prunkdump/GNUVario-TTGO-T5/boitier 3D/Ecran 1.54''/Plan boitier GNU VARIO.pdf

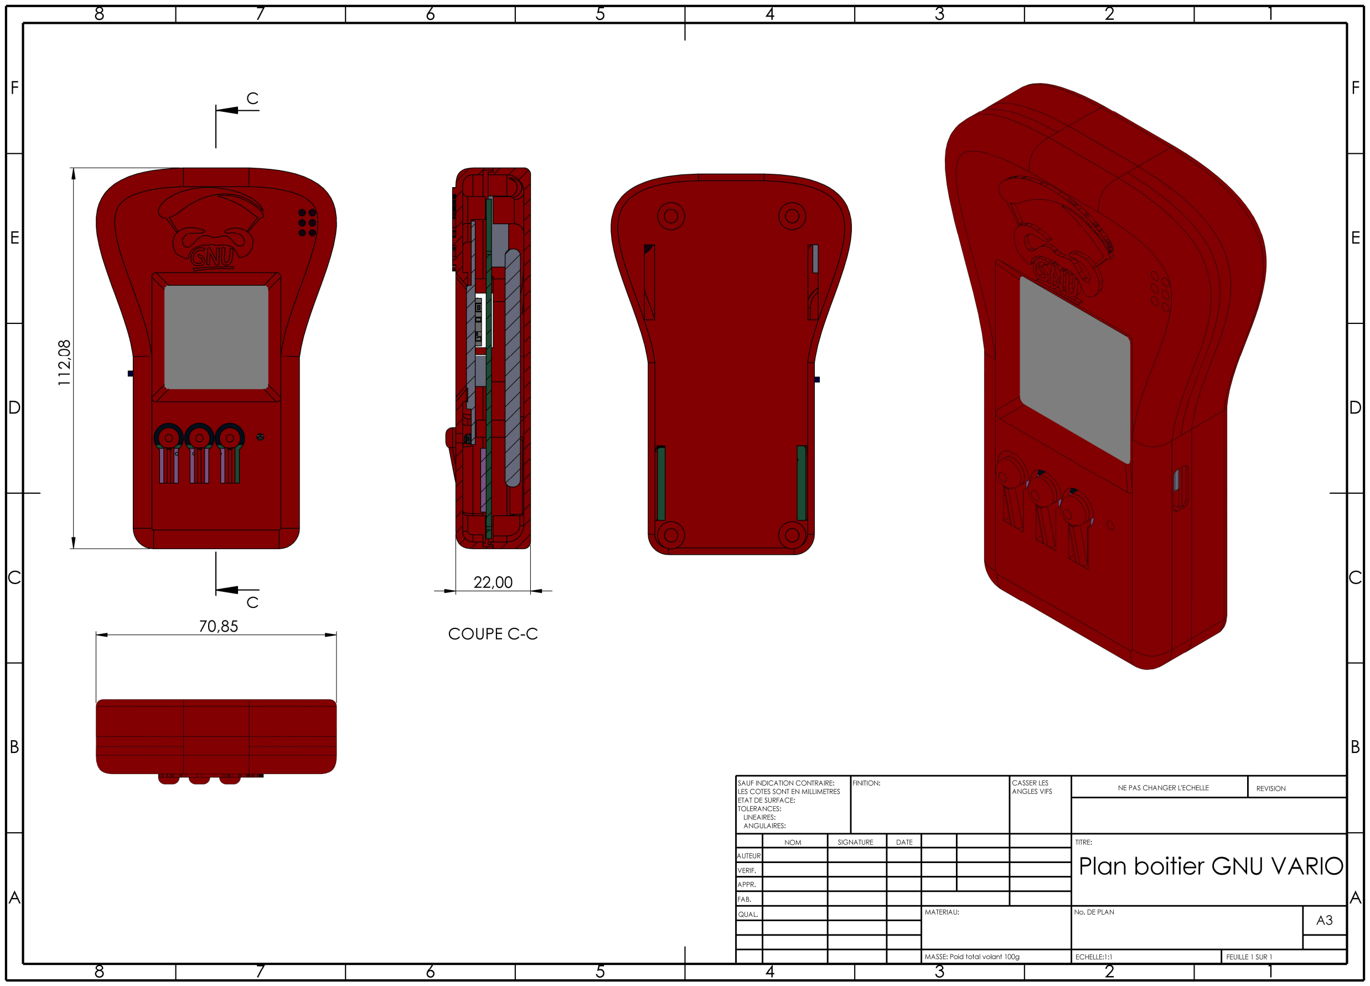
[picture p13: page 1]
