prunkdump/GNUVario-TTGO-T5/boitier 3D/Ecran 1.54''/20190728_134155_resized.jpg

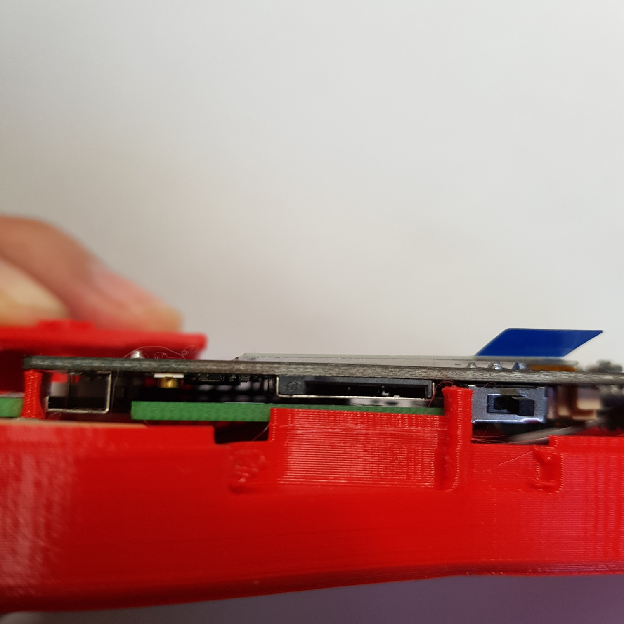
boitier 3D/Ecran 1.54''/20190728_134155_resized.jpg
