prunkdump/GNUVario-TTGO-T5/boitier 3D/Ecran 1.54''/Boitier arrière.jpg

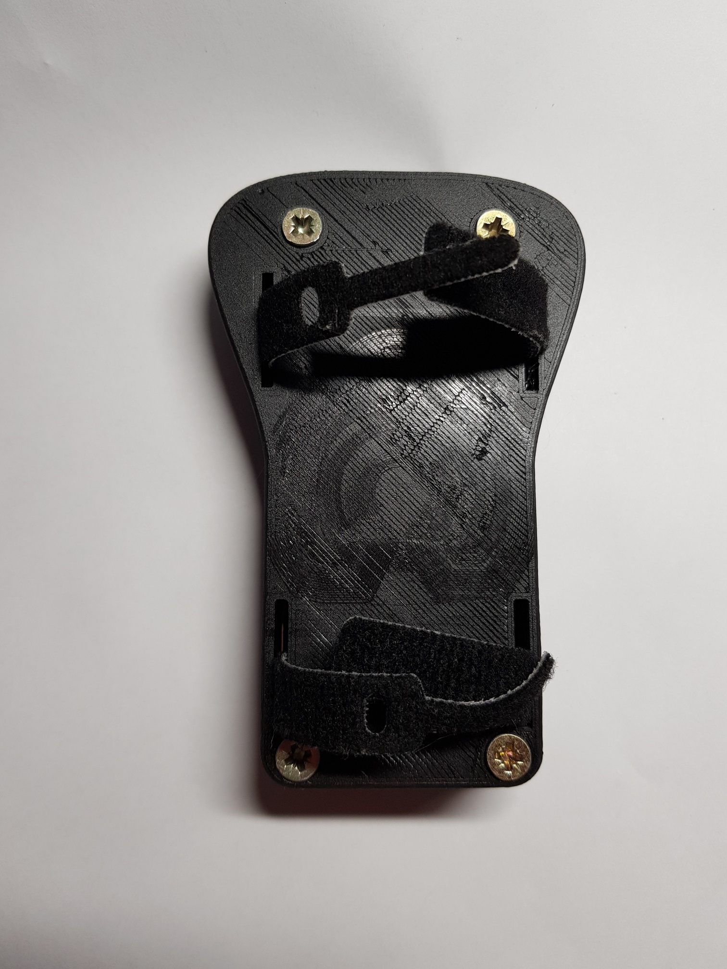
boitier 3D/Ecran 1.54''/Boitier arrière.jpg
