prunkdump/GNUVario-TTGO-T5/boitier 3D/Ecran 1.54''/Boitier avant.jpg

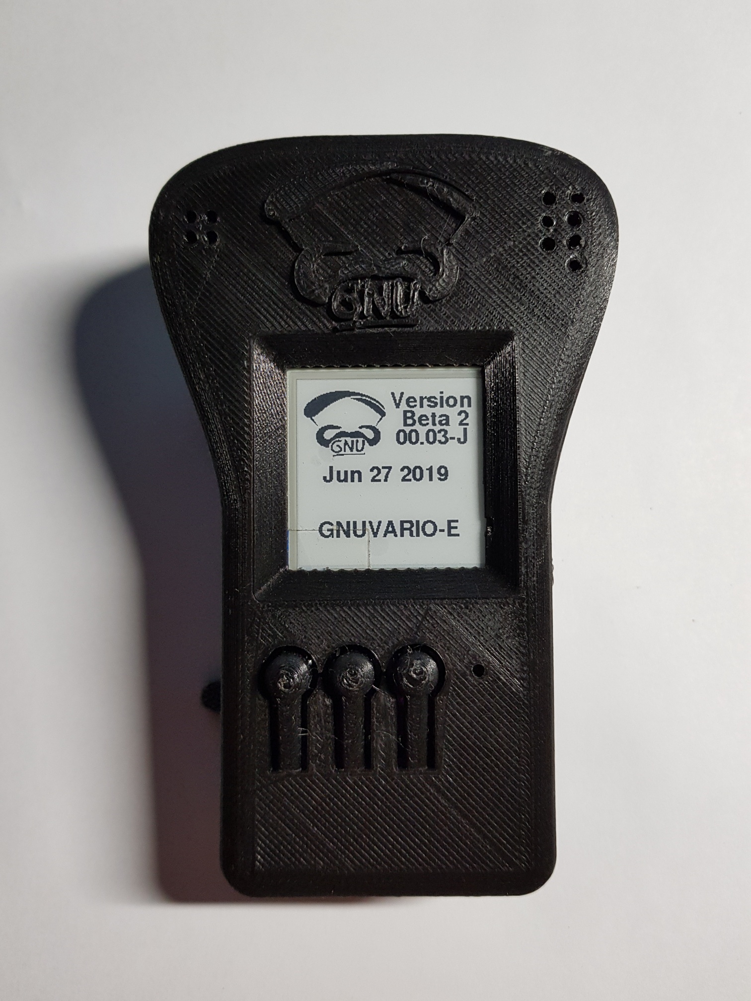
boitier 3D/Ecran 1.54''/Boitier avant.jpg
