prunkdump/GNUVario-TTGO-T5/boitier 3D/Ecran 1.54''/boitier tranche.jpg

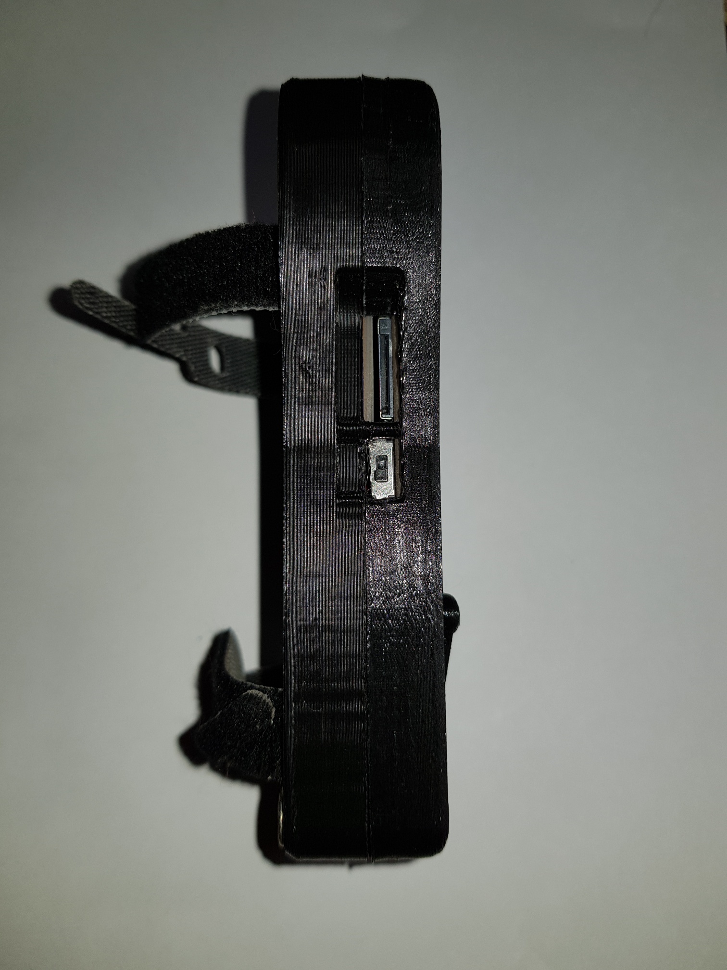
boitier 3D/Ecran 1.54''/boitier tranche.jpg
