prunkdump/GNUVario-TTGO-T5/boitier 3D/Ecran 1.54''/Fashion week.jpg

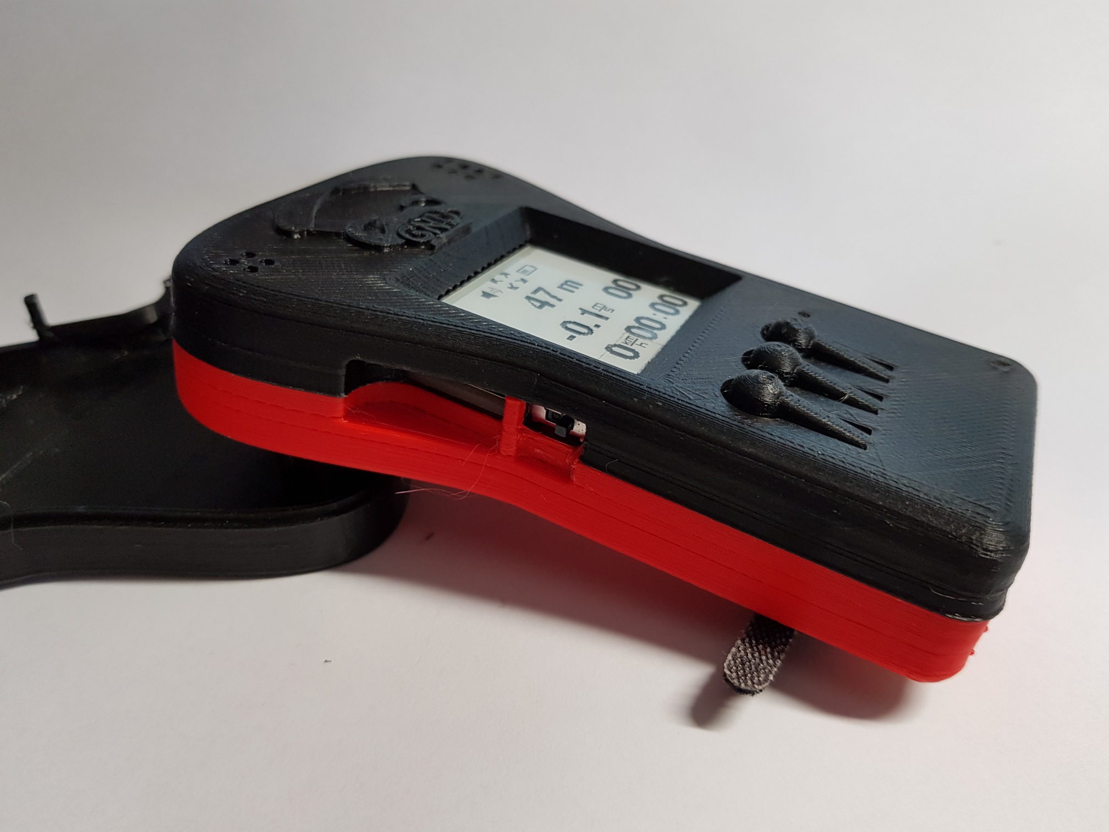
boitier 3D/Ecran 1.54''/Fashion week.jpg
