prunkdump/GNUVario-TTGO-T5/boitier 3D/Ecran 1.54''/Gnu bottom case/vis plastique.jpg

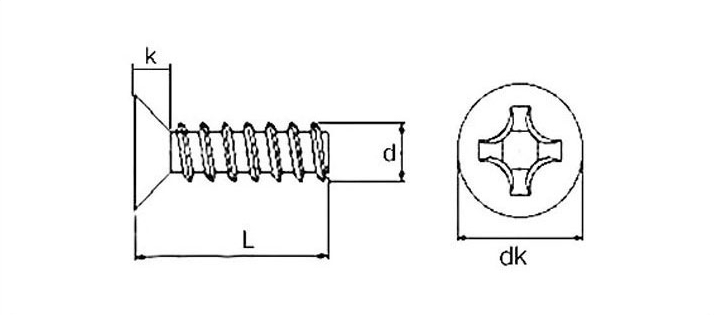
boitier 3D/Ecran 1.54''/Gnu bottom case/vis plastique.jpg
