prunkdump/GNUVario-TTGO-T5/boitier 3D/Ecran 1.54''/Support carte antenne.jpg

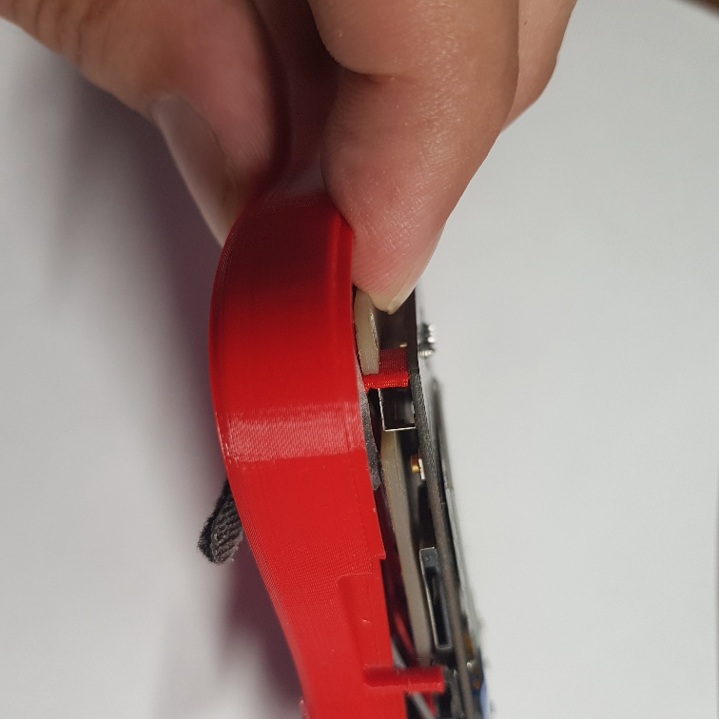
boitier 3D/Ecran 1.54''/Support carte antenne.jpg
