prunkdump/GNUVario-TTGO-T5/boitier 3D/Ecran 1.54''/Support carte pour soulager les boutons.jpg

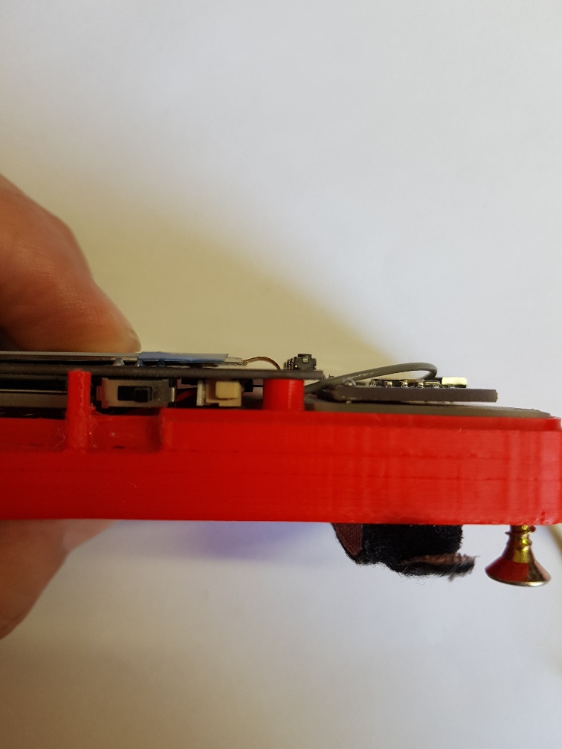
boitier 3D/Ecran 1.54''/Support carte pour soulager les boutons.jpg
