prunkdump/GNUVario-TTGO-T5/boitier 3D/Ecran 2.9'' portrait/Boitier 2.9 élévateurs.jpg

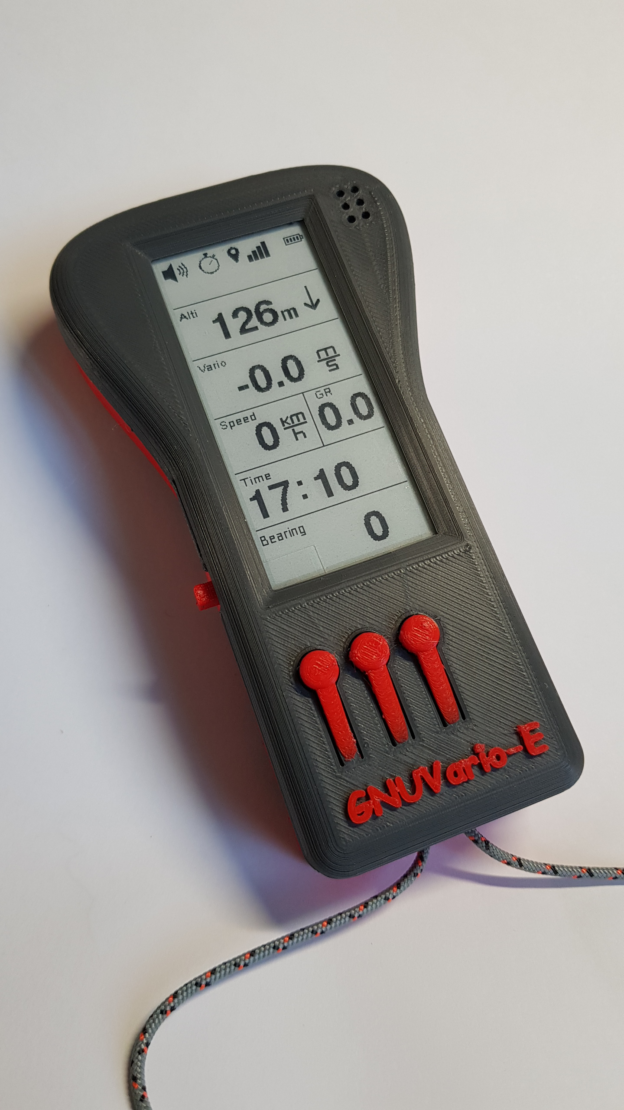
boitier 3D/Ecran 2.9'' portrait/Boitier 2.9 élévateurs.jpg
