prunkdump/GNUVario-TTGO-T5/boitier 3D/Ecran 2.9''/thumbnail_20190925_140538_resized.jpg

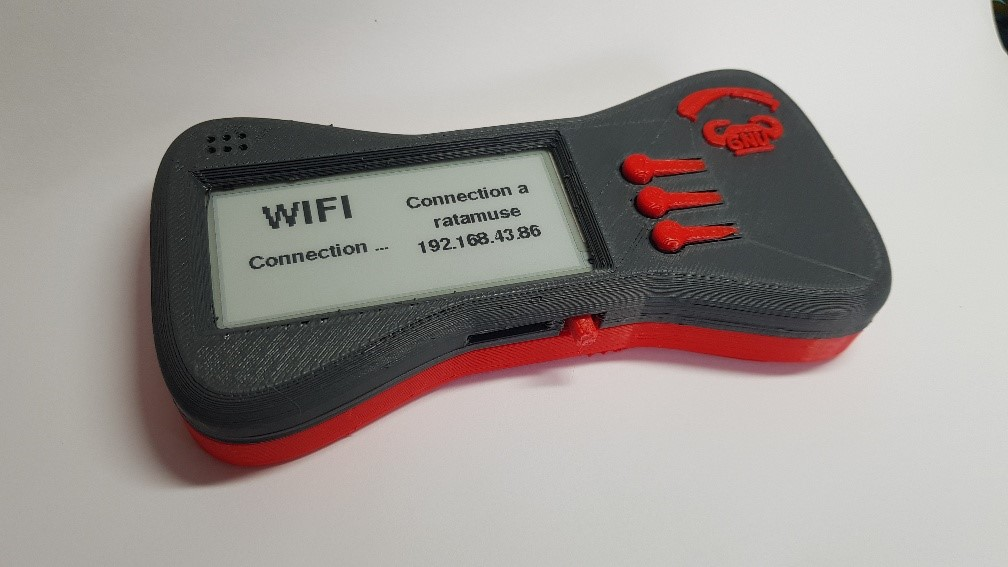
boitier 3D/Ecran 2.9''/thumbnail_20190925_140538_resized.jpg
