prunkdump/GNUVario-TTGO-T5/boitier 3D/Ecran 2.9''/thumbnail_20190925_141046_resized.jpg

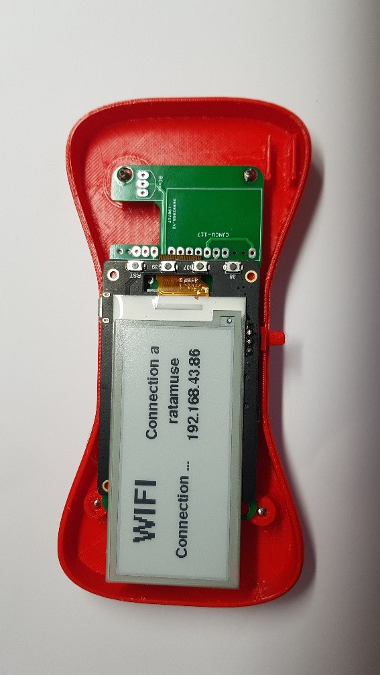
boitier 3D/Ecran 2.9''/thumbnail_20190925_141046_resized.jpg
