prunkdump/GNUVario-TTGO-T5/PCB/20191011_115533_resized.jpg

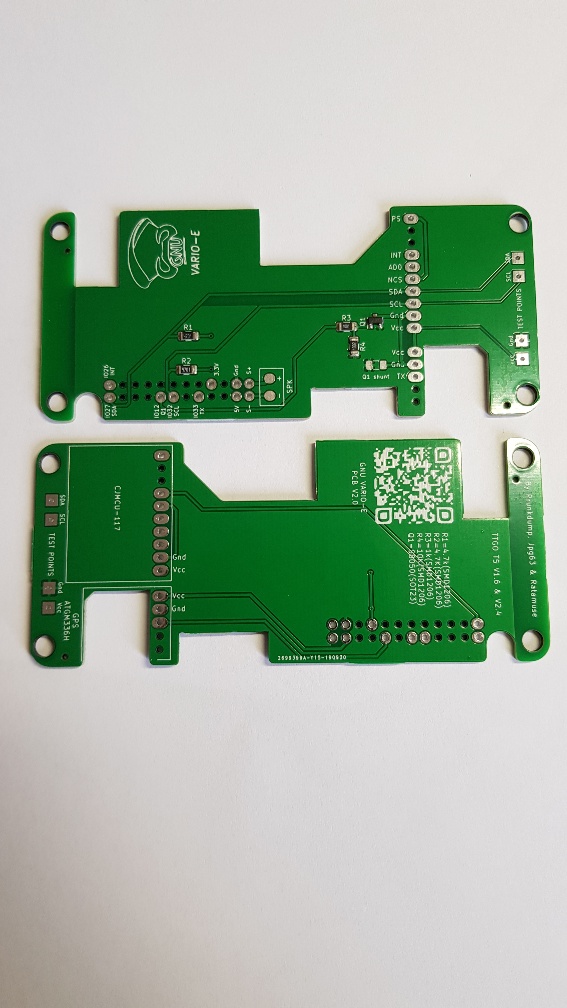
PCB/20191011_115533_resized.jpg
