prunkdump/GNUVario-TTGO-T5/PCB/Gnu Vario TTGO T5 V2 back.jpg

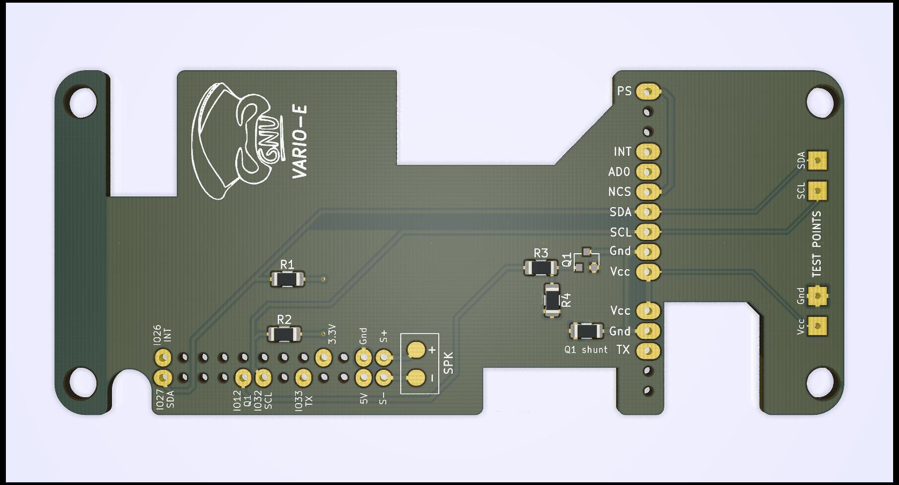
PCB/Gnu Vario TTGO T5 V2 back.jpg
