prunkdump/GNUVario-TTGO-T5/PCB/Gnu Vario TTGO T5 V2 front.jpg

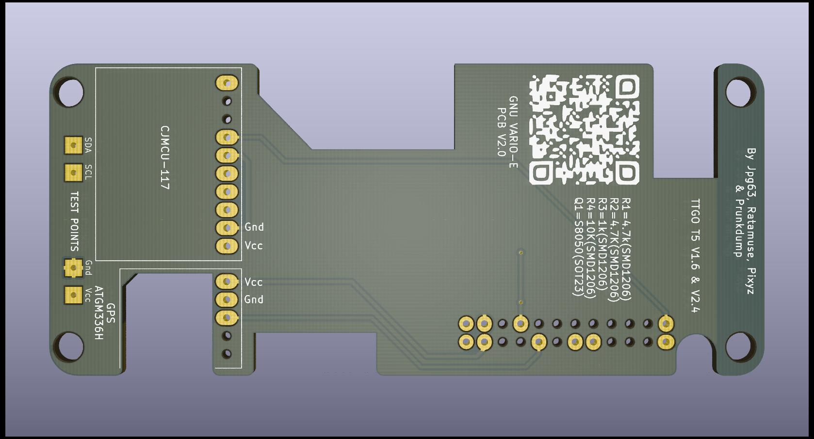
PCB/Gnu Vario TTGO T5 V2 front.jpg
