prunkdump/GNUVario-TTGO-T5/PCB/KiCad GNU Vario E V1.12/Pictures/PCB Back.jpeg

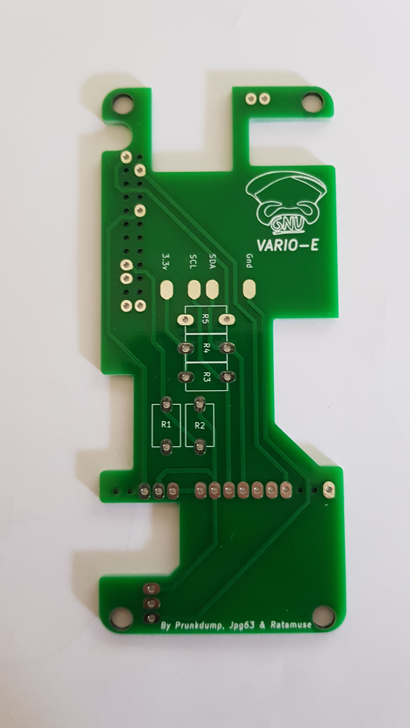
PCB/KiCad GNU Vario E V1.12/Pictures/PCB Back.jpeg
