prunkdump/GNUVario-TTGO-T5/PCB/PCB arrière.jpg

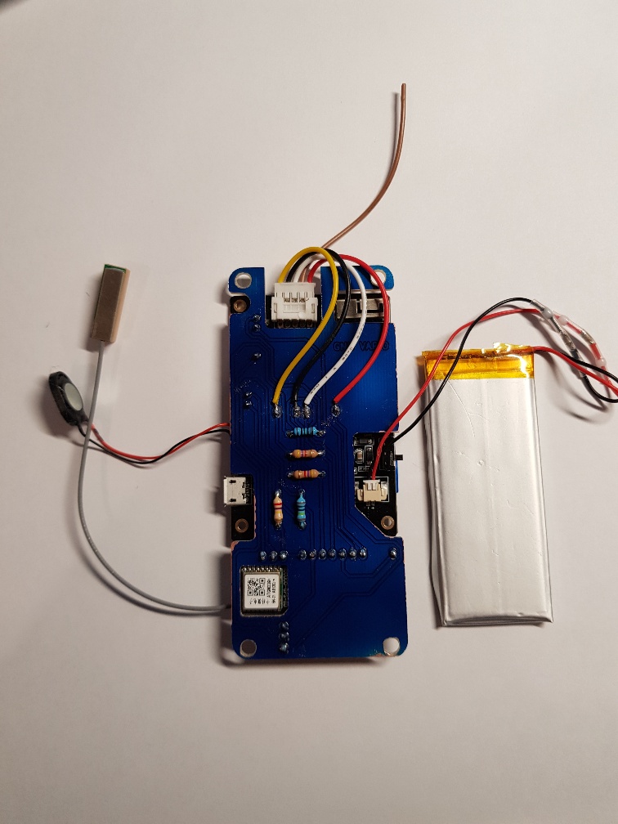
PCB/PCB arrière.jpg
