prunkdump/GNUVario-TTGO-T5/PCB/PCB avant.jpg

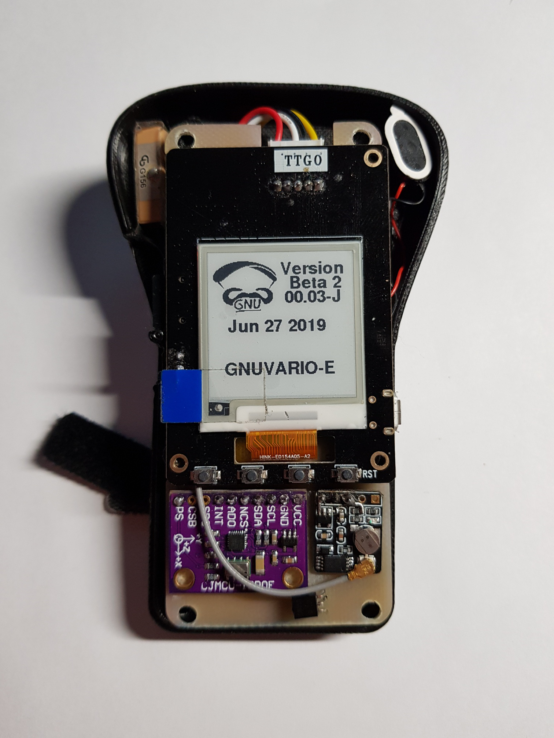
PCB/PCB avant.jpg
