prunkdump/GNUVario-TTGO-T5/PCB/PCB back.jpg

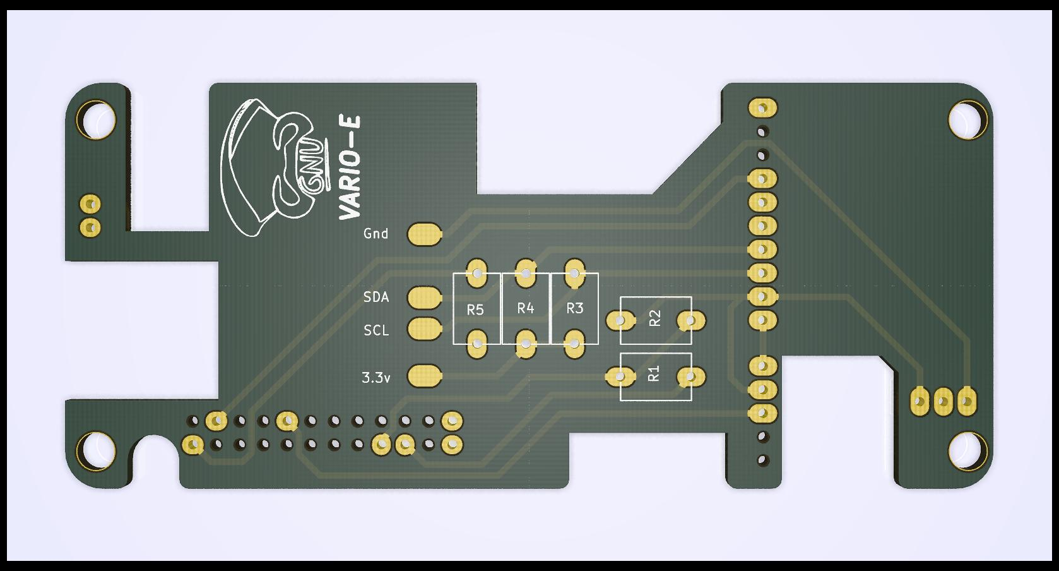
PCB/PCB back.jpg
