prunkdump/GNUVario-TTGO-T5/PCB/PCB front.jpg

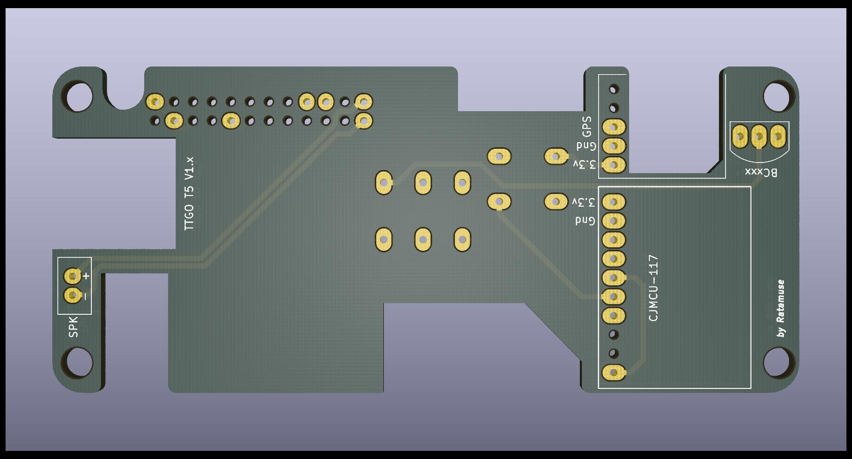
PCB/PCB front.jpg
