prunkdump/GNUVario-TTGO-T5/PCB/placement transistor.jpg

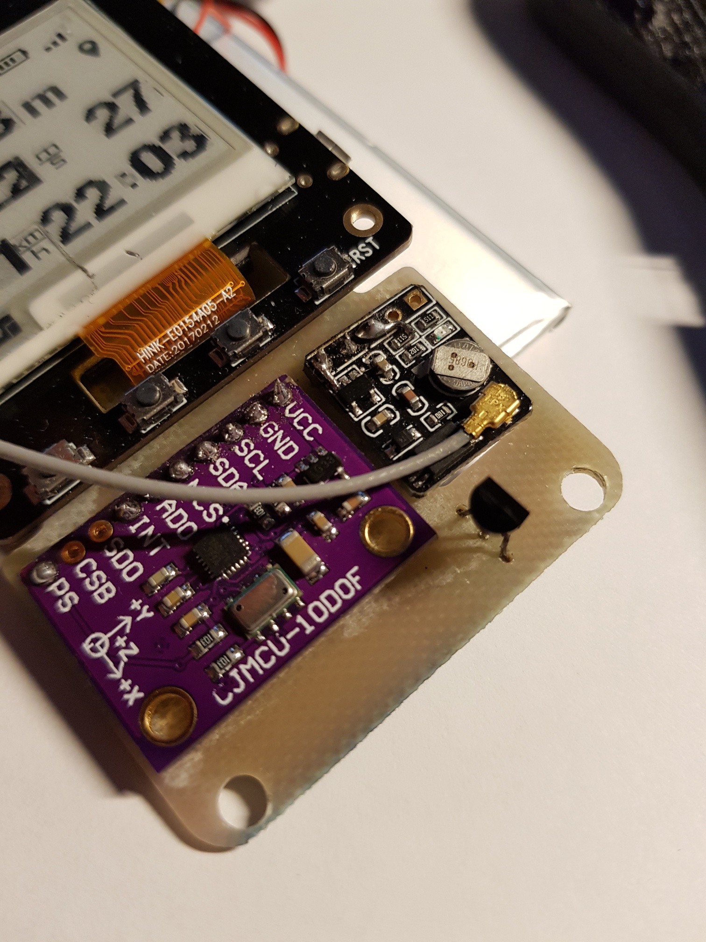
PCB/placement transistor.jpg
