prunkdump/GNUVario-TTGO-T5/Photos/20191012_085850.jpg

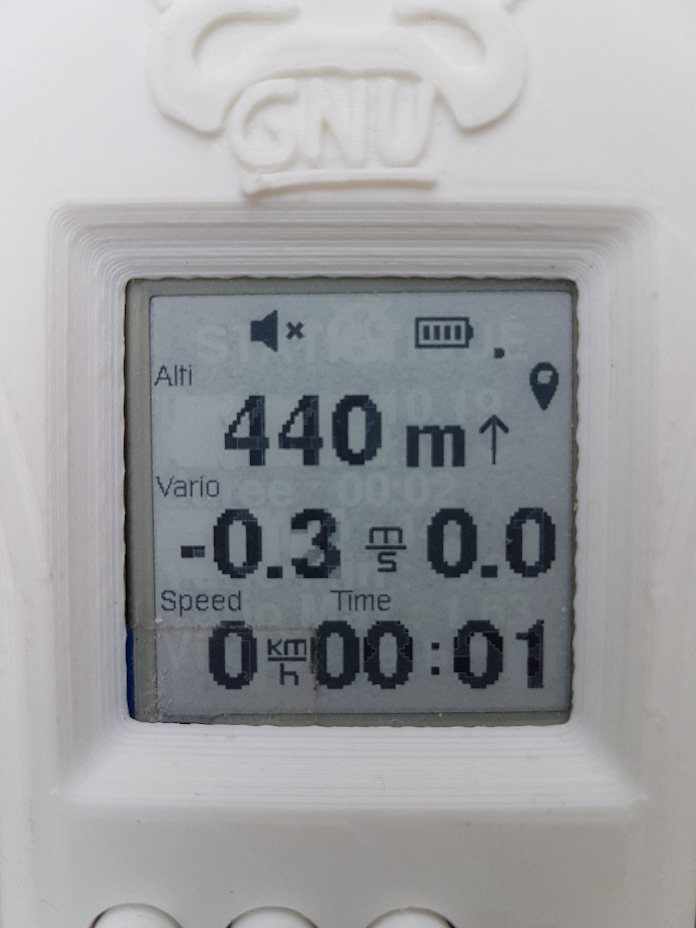
Photos/20191012_085850.jpg
