prunkdump/GNUVario-TTGO-T5/Photos/Case/20190922_080627.jpg

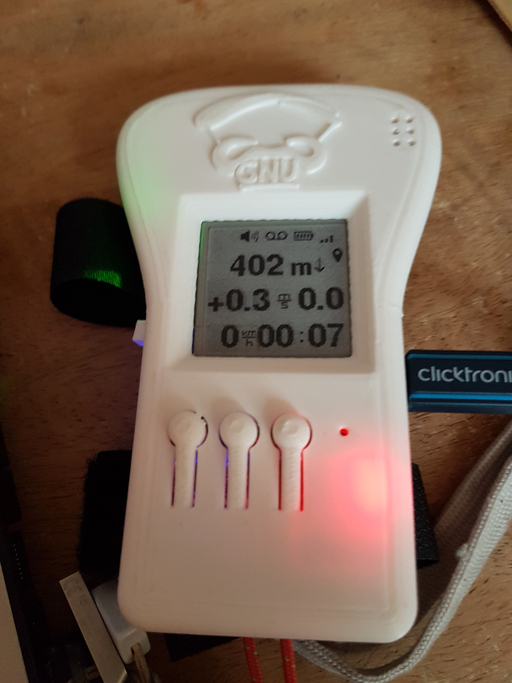
Photos/Case/20190922_080627.jpg
