prunkdump/GNUVario-TTGO-T5/Photos/Case/20191103_104739_resized.jpg

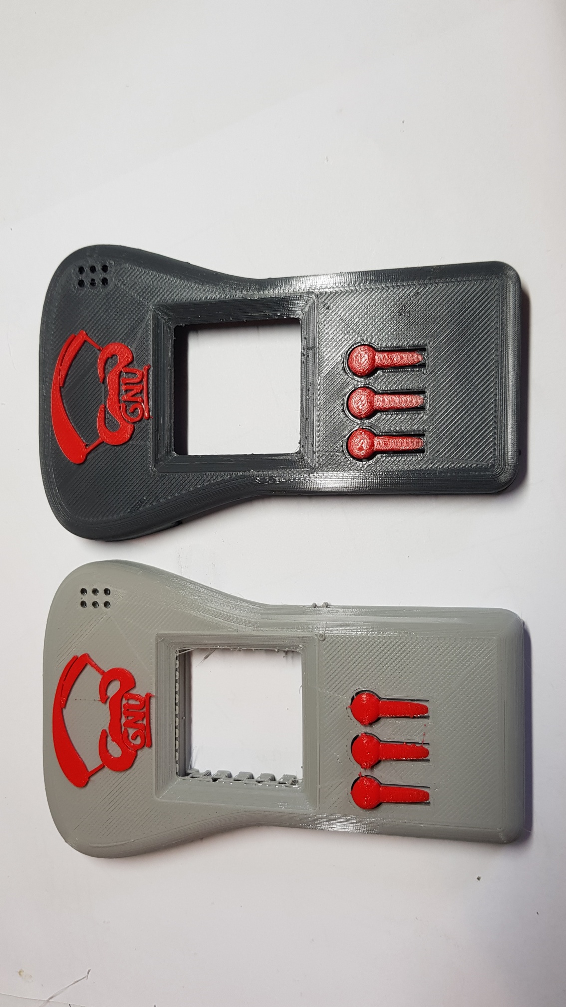
Photos/Case/20191103_104739_resized.jpg
