prunkdump/GNUVario-TTGO-T5/Photos/Case/20191105_001156_resized.jpg

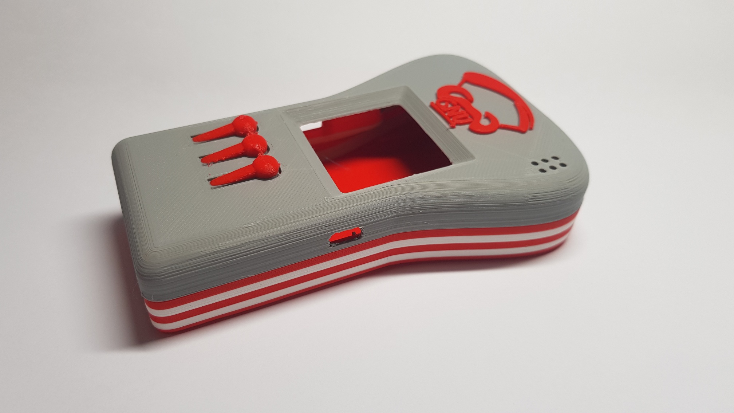
Photos/Case/20191105_001156_resized.jpg
