prunkdump/GNUVario-TTGO-T5/Photos/Case/20191105_001506_resized.jpg

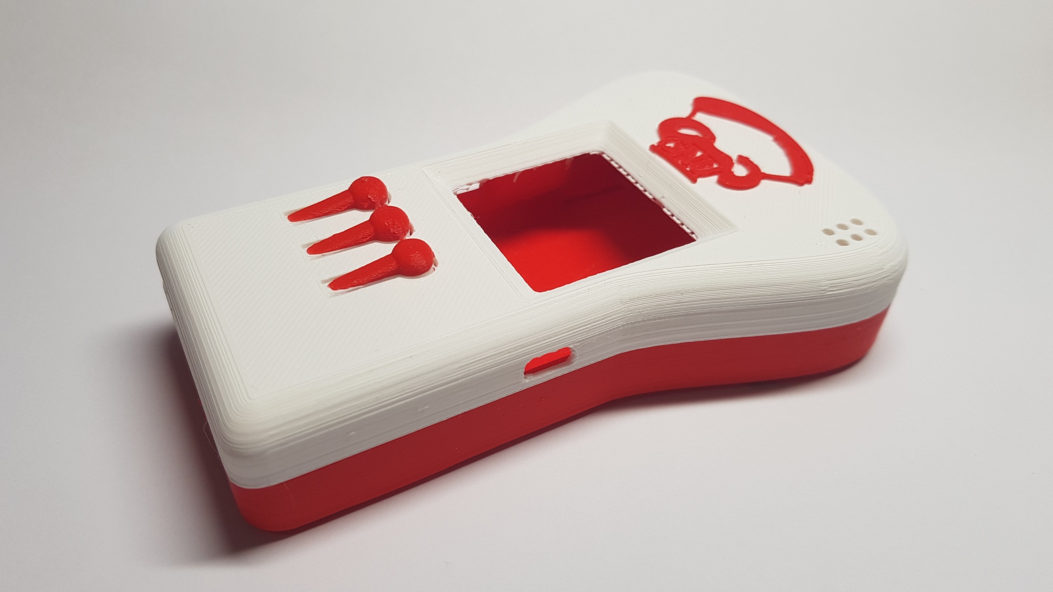
Photos/Case/20191105_001506_resized.jpg
