prunkdump/GNUVario-TTGO-T5/Photos/Case/Fashion week Rouge gris.jpg

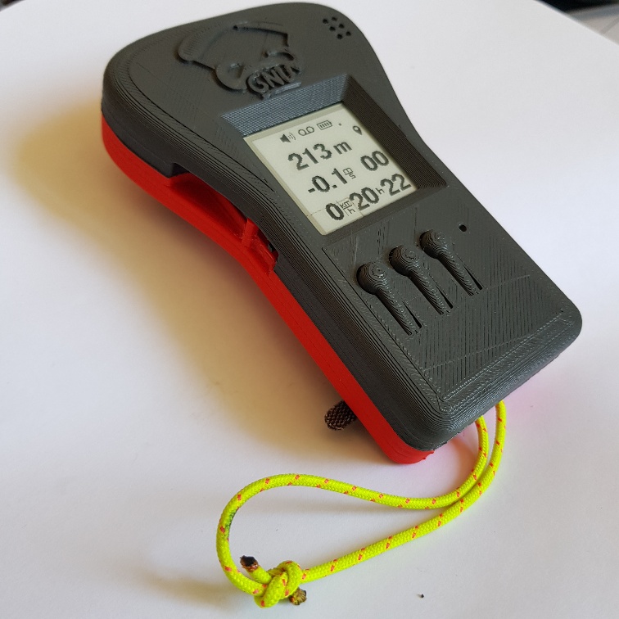
Photos/Case/Fashion week Rouge gris.jpg
