prunkdump/GNUVario-TTGO-T5/Photos/V1/20190727_112918.jpg

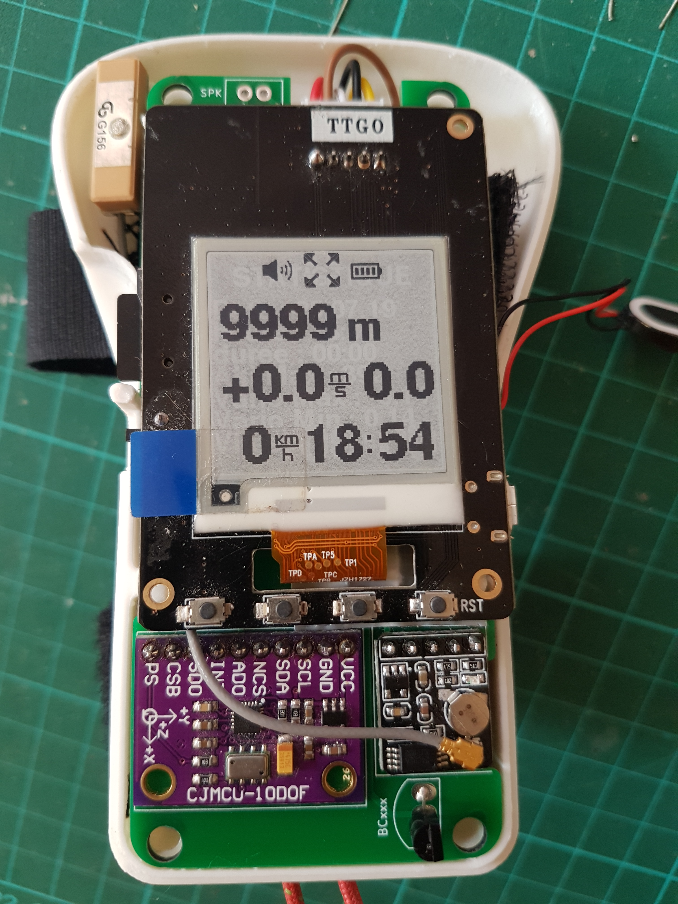
Photos/V1/20190727_112918.jpg
