prunkdump/GNUVario-TTGO-T5/PCB/PCB soldered.jpg

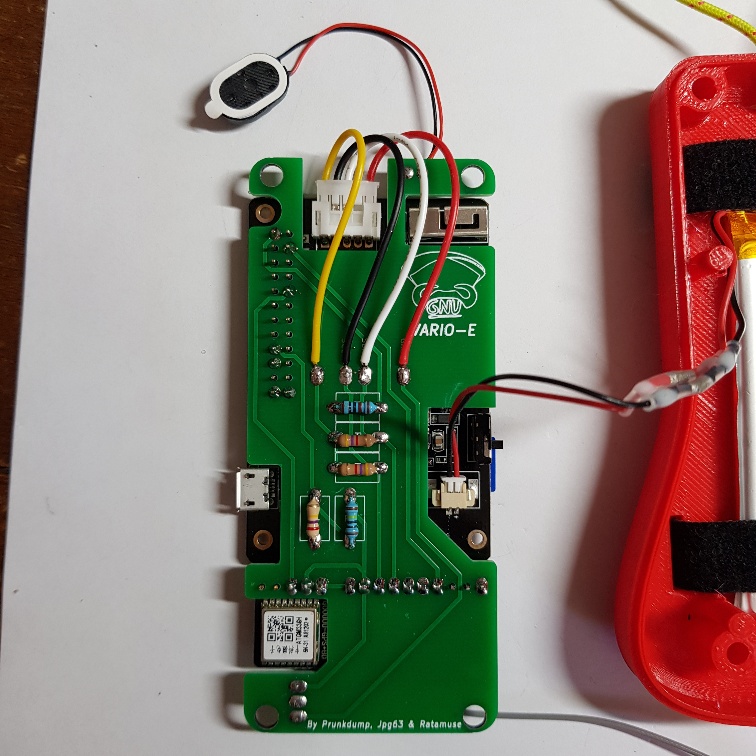
PCB/PCB soldered.jpg
