prunkdump/GNUVario-TTGO-T5/PCB/Printing Impression Schématique.jpg

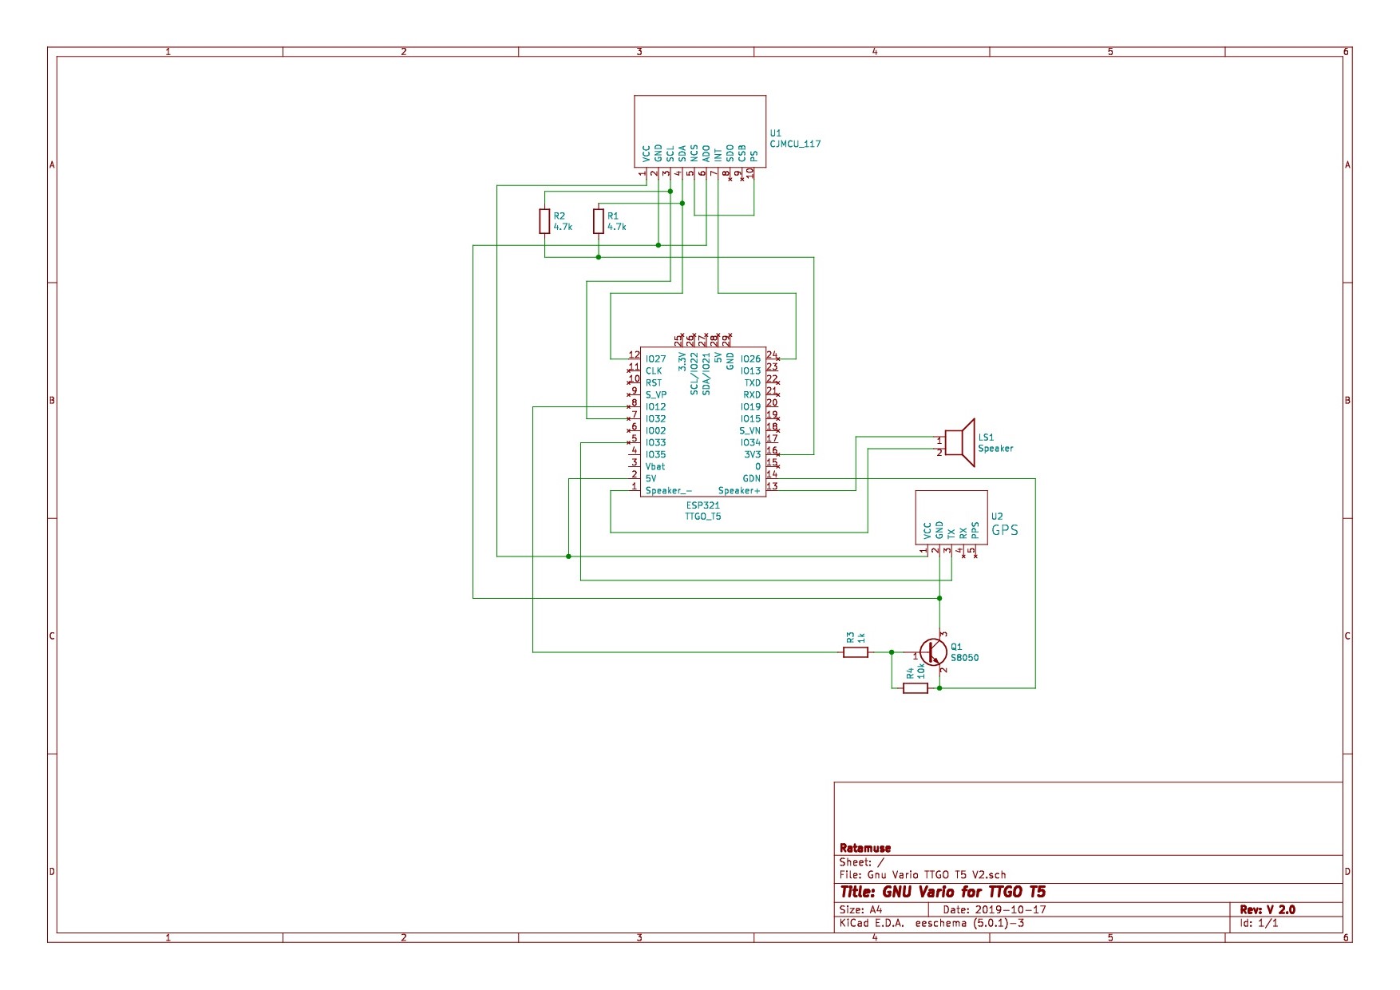
PCB/Printing Impression Schématique.jpg
