prunkdump/GNUVario-TTGO-T5/PCB/PCB V1.10.pdf

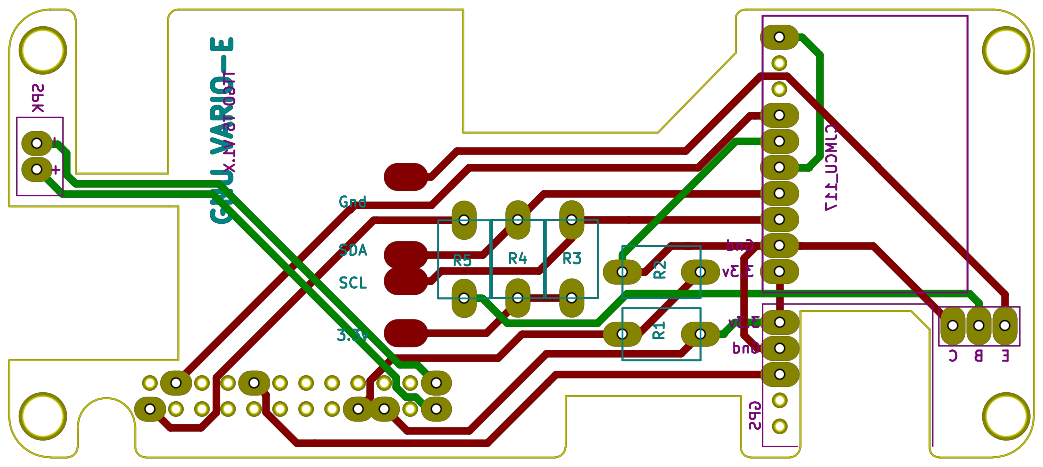
[picture p97: page 1]
