prunkdump/GNUVario-TTGO-T5/PCB/Schéma filaire PCB.pdf

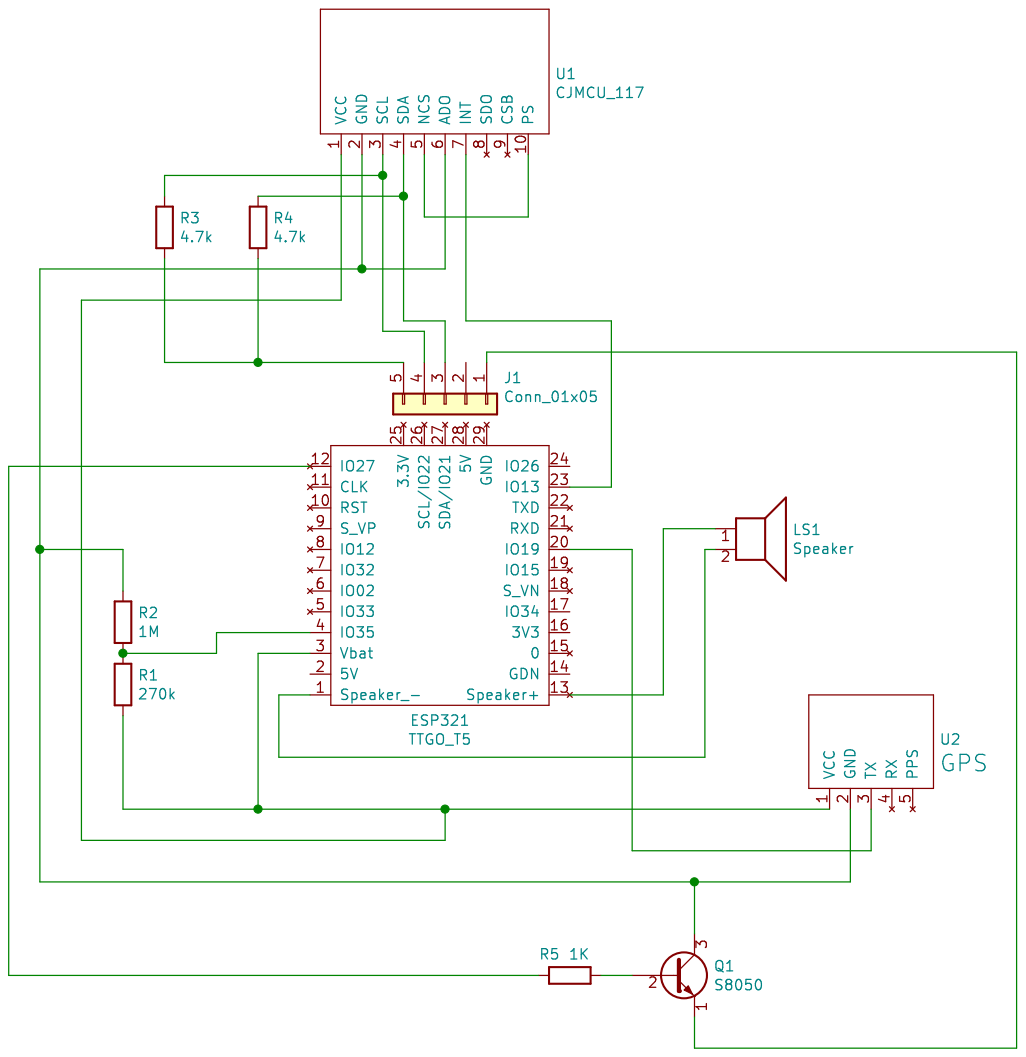
[picture p98: page 1]
