prunkdump/GNUVario-TTGO-T5/PCB/KiCad GNU Vario E V1.12/Schémas PCB/Schéma filaire.pdf

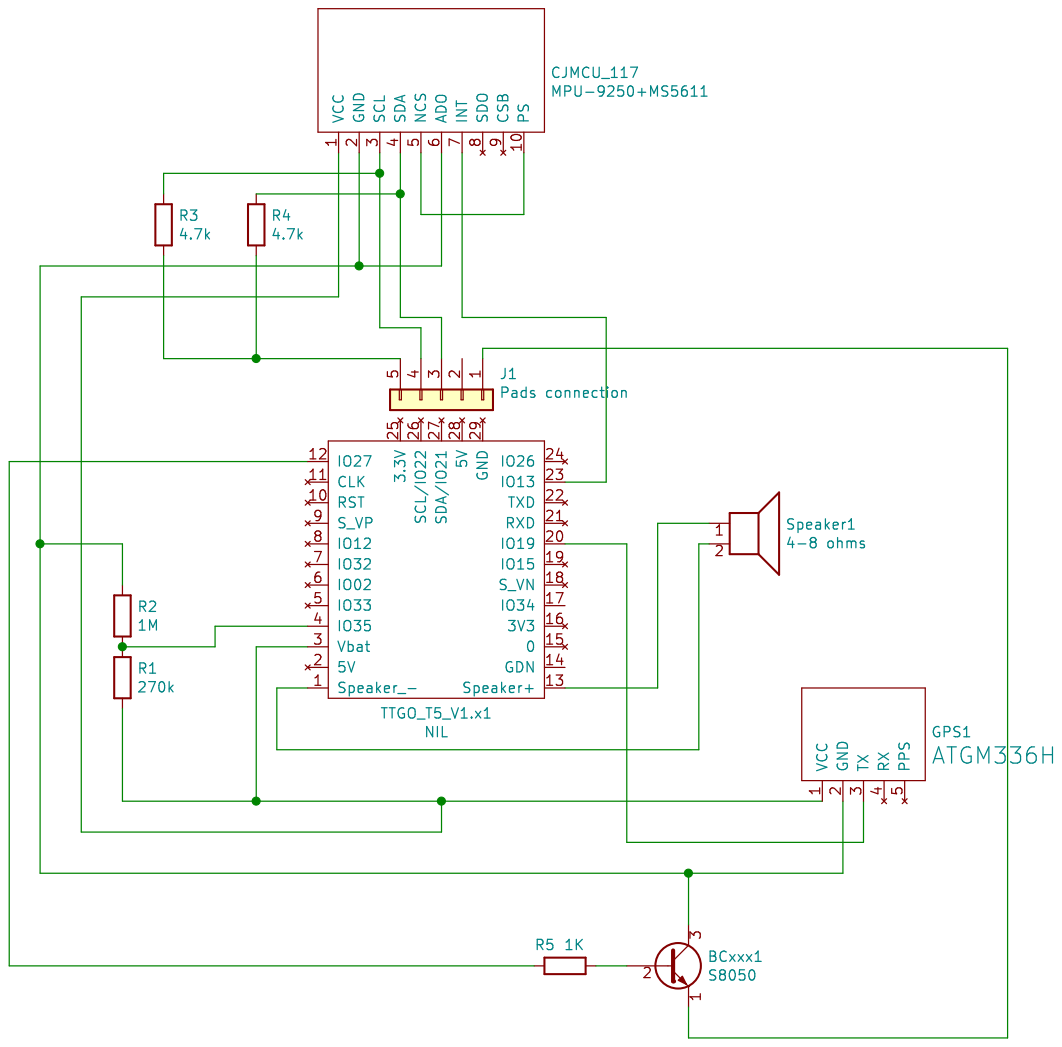
[picture p99: page 1]
