prunkdump/GNUVario-TTGO-T5/PCB/KiCad GNU Vario E V1.12/Schémas PCB/Schéma PCB.pdf

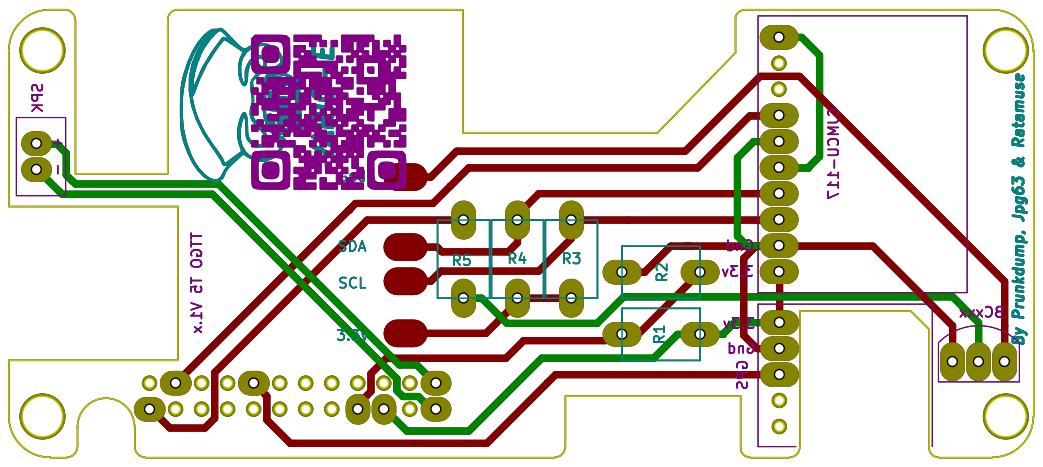
[picture p100: page 1]
