prunkdump/GNUVario-TTGO-T5/Sources/Beta Code/PlatformIO/Projects/GnuVarioE-master/src/HardwareConfig/HardwareConfigESP32.h

/* HardwareConfig -- 
 *
 * Copyright 2019 Jean-philippe GOI
 * 
 * HardwareConfig pour ESP32.
 *
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
 * You should have received a copy of the GNU General Public License
 * along with this program.  If not, see <https://www.gnu.org/licenses/>.
 */

/*********************************************************************************/
/*                                                                               */
/*                           HardwareConfig                                      */
/*                                                                               */
/*  version    Date     Description                                              */
/*    1.0    03/06/19                                                            */
/*    1.0.1  24/06/19   Ajout define VARIOMETER_POWER_ON_DELAY 									 */
/*    1.0.2  19/08/19   Correstions mineures                                     */
/*    1.0.3  20/08/19   Ajout version PCB  PCB_VERSION                           */
/*    1.0.4  30/08/19   Ajout AUDIO_AMP_MODE_LOW, AUDIO_AMPLI_LOWPOWER		  		 */
/*    1.0.5  10/09/19   Ajout VARIO_SDA_PIN, VARIO_SCL_PIN 											 */
/*		1.0.6	 19/09/19   Modification parametrage en fonction des PCBs            */
/*    1.0.7  06/10/19   Deplacement resolution d'ecran dans hardwareConfig.h     */
/*    1.0.8  27/06/20   Ajoit gestion I2S                                        */
/*    1.0.9  05/10/20   Ajout PCB V3                                             */
/*                                                                               */
/*********************************************************************************/


/*
*****************
MPU 9250 / MS5611
*****************
 
SDA_PIN 	IO21
SCL_PIN 	IO22
INT       IO32

*******************
Ecran EPaper 1.54''
*******************

CS/SS 		IO5
DC 				IO17
RST 			IO16
BUSY 			IO04

MOSI			IO15
MISO			IO02
SCK				IO14

*******
SDCard
*******

mySD.h

M5Stack.h

CS 			IO13
MOSI		IO15
MISO		IO02
SCK			IO14

*********
Boutons
*********

M4Stack.h

Bouton A	IO38
Bouton B	IO37
Bouton C	IO39

************
Speaker
************

PWM/DAC		IO25
Enable 		IO19		V2.4

 NS4148, http://www.chipsourcetek.com/Uploads/file/20151207193630_0605.pdf amplificateur audio mono 3W - Classe D connecté sur la pin GPIO 25

(XT_DAC_Audio) for ESP32  http://www.xtronical.com/the-dacaudio-library-download-and-installation/ 

PWM/DAC	IO26		optional ampli class D
Enable	IO34	enable optional ampli class D

******************
GPS
******************

RX	IO19		//IO33 V2.4

******************************
Lecture de la charge batterie
******************************

tension  IO35	

            vbat
             |
            100k
             |
      IO35 ---
             |
            100k
             |
            GND

EEprom

IGC Header			0x00		195+2		0xC8
Sounnd volume   0xC8    1+2     0xD0
Fly stat        0xD0		26+2

*/


#ifndef _HARDWARECONFIGESP32_H_
#define _HARDWARECONFIGESP32_H_

#if defined(ESP32)

/* Version PCB 															 */
/* 0 pas de PCB definit										 	 */
/* 1 PCB V1 pour TTGO-T5 version 1.64''   	 */
/* 2 PCB V2 pour TTGO-T5 version 1.64 et 2.9 */
/* 3 PCB V3 pour TTGO-T5 version 2.9''       */

#if (VARIOVERSION == 154) 
#define PCB_VERSION 1
#elif ((VARIOVERSION == 290) || (VARIOVERSION == 291) || (VARIOVERSION == 254)) 
#define PCB_VERSION 2
#elif ((VARIOVERSION == 390) || (VARIOVERSION == 391)) 
#define PCB_VERSION 3
#else
#define PCB_VERSION 0
#endif

/******************************/
/*            SCREEN          */
/******************************/

/* Set the pins used for Screen modules */

#define VARIOSCREEN_CS_PIN 5    //SS
#define VARIOSCREEN_DC_PIN 17
#define VARIOSCREEN_RST_PIN 16
#define VARIOSCREEN_BUSY_PIN 4

/****************************/
/*           SDCARD         */
/****************************/

#define SDCARD_CS_PIN   13
#define SDCARD_MOSI_PIN 15
#define SDCARD_MISO_PIN 2
#define SDCARD_SCK_PIN  14

// #define SDFAT_LIB

/***************************/
/*        LED              */
/***************************/

#if (PCB_VERSION == 0)
#define pinLED 22

#define LED_ON() 		   {GPIO.out_w1ts = (1 << (pinLED));}
#define LED_OFF()		   {GPIO.out_w1tc = (1 << (pinLED));}

#ifndef LED_BUILTIN
#define LED_BUILTIN pinLED
#endif

#endif

/****************************/
/*           Buttons        */
/****************************/

#define VARIOBTN_LEFT_PIN 38
#define VARIOBTN_CENTER_PIN 37
#define VARIOBTN_RIGHT_PIN 39

#define BTN_A 0
#define BTN_B 1
#define BTN_C 2
#define BUTTON_A 0
#define BUTTON_B 1
#define BUTTON_C 2

#define BUTTON_A_PIN 38
#define BUTTON_B_PIN 37
#define BUTTON_C_PIN 39

#define BUTTON_DEEP_SLEEP GPIO_NUM_37
#define GPIO_BUTTON_A GPIO_NUM_38
#define GPIO_BUTTON_C GPIO_NUM_39

/****************/
/*     TENSION  */
/****************/

// The voltage divisor 

#define VOLTAGE_DIVISOR_PIN 35  //ADC1_CH7 (GPIO 35)
#define VOLTAGE_RESOLUTION  4096.0f
#define VOLTAGE_DIVISOR_VALUE 2  //100k et 100k

/*************************/
/*        GPS            */
/*************************/

#if (PCB_VERSION == 2)
	// PCB 2
#define pinGpsRXD  (33)
	
/* GPS / bluetooth pins */
#define SERIAL_NMEA_RX_PIN 33
#define SERIAL_NMEA_TX_PIN 34

#elif (PCB_VERSION == 3)
	// PCB 3
#define pinGpsRXD  (33)
	
/* GPS / bluetooth pins */
#define SERIAL_NMEA_RX_PIN 33
#define SERIAL_NMEA_TX_PIN 34

#else
	
#define pinGpsRXD  (19)
	
/* GPS / bluetooth pins */
#define SERIAL_NMEA_RX_PIN 19
#define SERIAL_NMEA_TX_PIN 33
#endif	

#define pinGpsTXD  (-1)
#define pinGpsRTS  (-1)
#define pinGpsCTS  (-1)

/* The bauds rate used by the GPS and Bluetooth modules. */
/* GPS and bluetooth need to have the same bauds rate.   */
#define GPS_BLUETOOTH_BAUDS 9600

#define GPS_UART_NUM          UART_NUM_1
//#define UART_RX_BUFFER_SIZE   512
#define UART_RX_BUFFER_SIZE   256


/*************************/
/*         AUDIO         */
/*************************/

//#define AUDIO_AMP_MODE_LOW					//Ampli activable sur un niveau bas - sortie = 0
#define AUDIO_AMPLI_LOWPOWER				//Activation/desactivation de l'ampli à chaque tone/notone (economie d'énergie)

#if (PCB_VERSION == 2)
	// PCB 2
#define PIN_AUDIO_AMP_ENA     19			//Enabled ampli class D
#define HAVE_AUDIO_AMPLI	
//#define AUDIO_AMP_MODE_LOW					

#elif (PCB_VERSION == 3)
	// PCB 3
#define PIN_AUDIO_AMP_ENA     19			//Enabled ampli class D
#define HAVE_AUDIO_AMPLI	
//#define AUDIO_AMP_MODE_LOW					

#else

#define PIN_AUDIO_AMP_ENA     12			//Enabled ampli class D
	
#endif

#define SPEAKER_PIN 					25			//or 26
#define TONE_PIN_CHANNEL 			0				// or 1

#define AUDIO_I2S_CONFIG
#define DAC_INTERNE     // Definit si le DAC interne est utilisé

#define I2S_NUM         (0)
#define I2S_BCK_IO      (26)  //(GPIO_NUM_13)   //BCLK
#define I2S_WS_IO       (25)  //(GPIO_NUM_15)   //LRC
#define I2S_DO_IO       (14) //(GPIO_NUM_21)   //DIN
#define I2S_DI_IO       (-1)

#define AUDIO_TYPE_INTERFACE
#define TONE 													// 1 pin PWM
//#define	TONEAC 											// 2 pins Push-Pull PWM
//#define	TONEDACCOSINE
//#define TONEXTDAC
//#define TONEDACTIMER
//#define TONEI2S

/*********************/
/* TWO WIRE settings */
/* MPU 9250 / MS5611 */
/*********************/

#if (PCB_VERSION == 2)
	// PCB 2
#define VARIO_TW_SDA_PIN 27
#define VARIO_TW_SCL_PIN 32
#elif (PCB_VERSION == 3)
	// PCB 3
#define VARIO_TW_SDA_PIN 27
#define VARIO_TW_SCL_PIN 32
#else
#define VARIO_TW_SDA_PIN 21
#define VARIO_TW_SCL_PIN 22
#endif

/* Set the freq */
#define VARIO_TW_FREQ 400000UL

/*********************/
/* MPU 9250 / MS5611 */
/*********************/

#if (PCB_VERSION == 2)
	// PCB 2
#define VARIO_SDA_PIN 27
#define VARIO_SCL_PIN 32	
#define VARIO_MPU_INT_PIN 26
#define GPIO_MPU_INT GPIO_NUM_26
#elif (PCB_VERSION == 3)
	// PCB 3
#define VARIO_SDA_PIN 27
#define VARIO_SCL_PIN 32	
#define VARIO_MPU_INT_PIN 26
#define GPIO_MPU_INT GPIO_NUM_26
#else
#define VARIO_SDA_PIN 21
#define VARIO_SCL_PIN 22
#endif

/*************************/
/*         POWER         */
/*************************/

#if (PCB_VERSION == 2)
	// PCB 2
#define POWER_PIN 12
#elif (PCB_VERSION == 3)
	// PCB 3
#define POWER_PIN 12
#else
#define POWER_PIN 27
#endif
#define POWER_PIN_STATE HIGH

/* time needed to power on all the devices */
#define VARIOMETER_POWER_ON_DELAY 2000

/*****************************/
/*         EEPROM            */
/*****************************/
//  IGC Header			0x00		195		0xC8
//  Sound volume		0xC8    1     0xD0
//  Fly Stat        0xD0    48X10 0x2B0     
//  Calibration     0x2C0   56 		0x2FA				(762)

/*****************************/
/*  IGC HEADER EEPROM        */
/*****************************/

#define IGC_SENTENCE_HEADER_EEPROM_ADDRESS 0x0 

/*****************************/
/*  EEPROM SOUND             */
/*****************************/

/* eeprom sound setting adresses */
#define SOUND_EEPROM_ADDR 0xC8

/*****************************/
/*  EEPROM STAT              */
/*****************************/
#define FLY_STAT_HEADER_EEPROM_ADDRESS 0xD0

/*****************************/
/*  EEPROM CALIBRATION       */
/*****************************/
#define CAL_MPU_HEADER_EEPROM_ADDRESS 0x108 //0x2C0

#endif
#endif
