prunkdump/GNUVario-TTGO-T5/Sources/Beta Code/PlatformIO/Projects/GnuVarioE-master/src/VarioData/VarioData.h

/* VarioData -- 
 *
 * Copyright 2020 MichelPa / Jpg63
 * 
 * This file is part of GnuVario-E.
 *
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
 * You should have received a copy of the GNU General Public License
 * along with this program.  If not, see <https://www.gnu.org/licenses/>.
 */

/* 
 *********************************************************************************
 *                                                                               *
 *                           VarioData                                           *
 *                                                                               *
 *  version    Date     Description                                              *
 *    1.0    22/03/20                                                            *
 *    1.0.1  25/03/20   Ajout dataAcquisition(void)                              *
 *        							compteurErrorMPU																				 *
 *    1.0.2  07/04/20   ajout updateBeeper(void)                                 *
 *    1.0.3  18/04/20   Ajour reglage du kalman                                  *
 *                      Ajout intégration vario                                  *
 *    1.0.4  08/05/20   Ajout getCap                                             *
 *    1.0.5  27/06/20   Ajout varioxbeeper                                       *
 *    1.0.6  30/07/20   Ajout gestion valeur maximum des données                 *
 *    1.0.7  27/09/20   Ajout test sur lecture des fichiers de config            *
 *                                                                               *
 *********************************************************************************
 */
 
#ifndef VARIO_DATA_H
#define VARIO_DATA_H

#include <HardwareConfig.h>
#include <kalmanvert.h>
//#include "VarioDataTwoWireScheduler.h"
#include <IntTW.h>
#include <ms5611TW.h>
#include <vertaccel.h>
#include <LightInvensense.h>
#include <TwoWireScheduler.h>
#include <sdcardHAL.h>
//#include <GPSSentence.h>

/*********************/
/*  AGL              */
/*********************/

#if defined(HAVE_SDCARD) && defined(HAVE_GPS)
#include <AglManager.h>
#endif //HAVE_SDCARD && HAVE_GPS

#include <FlightHistory.h>
#include <variostat.h>

#ifdef HAVE_GPS
		constexpr double historyGPSPeriodCountF = (double)(GPS_PERIOD) / 500.0;
		constexpr int8_t historyGPSPeriodCount = (int8_t)(0.5 + historyGPSPeriodCountF);
#endif

#define	GPSFIX_NOGPS		0				//no gps
#define GPSFIX_INIT			1				//time
#define GPSFIX_FIX			2				//gps fix
#define GPSFIX_RECORD 	3				//record data
#define GPSFIX_NORECORD	4				//no record file

#define STATE_PAGE_INIT 0
#define STATE_PAGE_VARIO 1
#define STATE_PAGE_CONFIG 2
#define STATE_PAGE_STAT 3
#define STATE_PAGE_GPSCAL 4
#define STATE_PAGE_WEBSERV 5
#define STATE_PAGE_CONFIG_SOUND 6
#define STATE_PAGE_DEEP_SLEEP 7
#define STATE_PAGE_CALIBRATION 8
#define STATE_PAGE_CALIBRATE 9

class VarioData
{
public:
    VarioData();
    void 		init(uint8_t version, uint8_t sub_version, uint8_t beta_code, String devname);
		void 		initKalman(double firstAlti);
		bool 		initSettings(bool Test_SD); 
		bool 		initLog(void); 
		bool 		initAGL(void);
		void 		initTime(void);

    void   	update();
		bool   	updateBluetooth();
		void   	updateGps();
		void    updateState();
		bool 		updateSpeed(void);
		void 		updateVoltage(void);
		void 		updateBeeper(void);

    double 	getVelocity();
    double 	getCalibratedAlti();
		double 	getClimbRate();
		double 	getTrend();
		int    	getStateTrend();
		uint8_t getVariometerState();
		int 		getCap();
		double  getSpeed();
		void    setCurrentHeight(double height);
		double  getCurrentHeight();
		void    setGpsAlti(double gpsalti);
		double  getGpsAlti();
		
		bool 	 	haveNewClimbRate();
				
		void 		createSDCardTrackFile(void);
		void 		enableflightStartComponents(void);
		
		int 		compteurGpsFix = 0;
		uint8_t gpsFix = 0;

		double  ratio = 0;

		long 		voltage = 0;
		
		unsigned long lastDisplayTimestamp, lastDisplayTimestamp2;

    boolean displayLowUpdateState = true;
    boolean displayUpdateState = true;

    VarioStat flystat;

    Kalmanvert kalmanvert;

/*********************/
/*  AGL              */
/*********************/

#ifdef AGL_MANAGER_H
		AglManager aglManager;
#endif

/************************************/
/* glide ratio / average climb rate */
/************************************/

/* two minutes history */
#ifdef HAVE_GPS
		SpeedFlightHistory<500, 120, historyGPSPeriodCount> history;
#else
		FlightHistory<500, 120> history;
#endif

		FlightHistory<50, 40> buzzerHistory;

private:
		unsigned long compteurErrorMPU = 0;
		int compteurBoucle = 0;


// DATA

		uint8_t Version;
		uint8_t Sub_Version;
		uint8_t Beta_Code;
		String  Devname;
    double 	firstAlti; 
		double 	velocity;				//KalmanVario
		double 	alti;						//Alti baro
		double 	calibratedAlti;	//KalmanAlti
		double 	temperature;
		double 	accel;
		double 	climbRate;
		bool   	haveNewClimbRateData = false;
		double 	trend;
		int 	 	stateTrend;		
		double 	climbRateBuzzer;
		bool   	haveNewClimbRateDataBuzzer = false;
		uint8_t variometerState;
		double 	currentSpeed  = 0;
		double 	gpsAlti = 0;
		double 	currentHeight = 0;
		
		bool 		CompteurStartFlyEnable 	= false;
		unsigned long	TimeStartFly;
		uint8_t	CompteurStartFly	= 0;
		bool		SpeedAvalable = false;
		bool    GpsAvalable   = false;
		unsigned long	TimeCapMesure = 0;		
		int 		bearing = 0;
		int 		moyCap = 0;
		int			nbMesureCap = 0;
		
		float constrainAngle360(float dta);
};

extern VarioData varioData;

/**********************/
/* SDCARD objects     */
/**********************/
extern int8_t sdcardState;
extern VarioSettings GnuSettings;

#endif //VARIO_DATA_H
