prunkdump/GNUVario-TTGO-T5/Sources/Beta Code/PlatformIO/Projects/GnuVarioE-master/src/eepromHAL/src/eepromHAL_M0.h

/*********************************************************************************/
/*                                                                               */
/*                           Libraries eepromHal_M0                              */
/*                                                                               */
/*  version    Date     Description                                              */
/*    1.0    05/02/19                                                            */
/*    1.1    09/07/19   Ajout init(size)                                         */
/*                                                                               */
/*********************************************************************************/

#ifndef eepromHAL_M0_h
#define eepromHAL_M0_h

#include <Arduino.h>
#include "eepromHAL.h"

#if defined(ARDUINO_ARCH_SAMD)

class EepromHal_zero : public EepromHal {

  public:

		void init(void);

		void init(int size);

    /**
     * Read an eeprom cell
     * @param address
     * @return value
     */
    uint8_t read(int address);

    /**
     * Write value to an eeprom cell
     * @param address
     * @param value
     */
    void write(int address, uint8_t value);

    /**
     * Update a eeprom cell
     * @param address
     * @param value
     */
    void update(int address, uint8_t value);

    /**
     * Check whether the eeprom data is valid
     * @return true, if eeprom data is valid (has been written at least once), false if not
     */
    bool isValid();

    /**
     * Write previously made eeprom changes to the underlying flash storage
     * Use this with care: Each and every commit will harm the flash and reduce it's lifetime (like with every flash memory)
     */
    void commit();

};

#define EepromHAL EepromHal_zero;
extern EepromHAL EEPROMHAL;

#endif //ARDUINO_ARCH_SAMD

#endif
	
	
