prunkdump/GNUVario-TTGO-T5/Sources/Beta Code/PlatformIO/Projects/GnuVarioE-master/src/eepromHAL/src/eepromHAL_PRO.cpp

/*********************************************************************************/
/*                                                                               */
/*                           Libraries eepromHal_PRO                             */
/*                                                                               */
/*  version    Date     Description                                              */
/*    1.0    06/02/19                                                            */
/*    1.1    09/07/19   Ajout init(size)                                         */
/*                                                                               */
/*********************************************************************************/

#include "eepromHAL.h"
#include "eepromHAL_PRO.h"
#include <Arduino.h>

#if defined(ARDUINO_AVR_PRO)
#include <EEPROM.h>

#include <DebugConfig.h>

/*#if not defined(DEBUG_H)
//Monitor Port 
#define SerialPort Serial

#define EEPROM_DEBUG

#endif*/

EepromHAL EEPROMHAL;

void EepromHal_pro::init(void) {}

void EepromHal_pro::init(int size) {}

uint8_t EepromHal_pro::read(int address)
{
  return EEPROM.read(address);
}

void EepromHal_pro::update(int address, uint8_t value)
{
  EEPROM.update(address, value);
}

void EepromHal_pro::write(int address, uint8_t value)
{
  EEPROM.write(address, value);
}

bool EepromHal_pro::isValid()
{
  return true;
}

void EepromHal_pro::commit()
{
}

#endif //ARDUINO_AVR_PRO
