prunkdump/GNUVario-TTGO-T5/Sources/Test Code/Test CJMCU 117/MPU9250_DMP_Quaternion/MPU9250_DMP_Quaternion.ino

/************************************************************
MPU9250_DMP_Quaternion
 Quaternion example for MPU-9250 DMP Arduino Library 
Jim Lindblom @ SparkFun Electronics
original creation date: November 23, 2016
https://github.com/sparkfun/SparkFun_MPU9250_DMP_Arduino_Library

The MPU-9250's digital motion processor (DMP) can calculate
four unit quaternions, which can be used to represent the
rotation of an object.

This exmaple demonstrates how to configure the DMP to 
calculate quaternions, and prints them out to the serial
monitor. It also calculates pitch, roll, and yaw from those
values.

Development environment specifics:
Arduino IDE 1.6.12
SparkFun 9DoF Razor IMU M0

Supported Platforms:
- ATSAMD21 (Arduino Zero, SparkFun SAMD21 Breakouts)
*************************************************************/

// https://learn.sparkfun.com/tutorials/9dof-razor-imu-m0-hookup-guide#using-the-mpu-9250-dmp-arduino-library
// https://www.hackster.io/donowak/esp32-mpu9250-3d-orientation-visualisation-467dc1

//https://create.arduino.cc/projecthub/30503/using-the-mpu9250-to-get-real-time-motion-data-08f011

//https://www.coordonnees-gps.fr/
//https://www.ngdc.noaa.gov/geomag/calculators/magcalc.shtml
// yam =-1.35;

//257  -793  324 -3  13  7

#include <MPU9250-DMP_SF_EXT.h>
#include <MS5611-Ext.h>
#include <HardwareConfig.h>
#include <DebugConfig.h>

#if !defined(SerialPort)
#define SerialPort Serial
#endif

MPU9250_DMP imu;

MS5611 ms5611;
double referencePressure;
long accelBias[3], gyroBias[3];

//#define SAVE_EEPROM

void setup() 
{
  SerialPort.begin(115200);

  delay(5000);
  
  // Initialize MS5611 sensor
  SerialPort.println("Initialize MS5611 Sensor");

#if defined(VARIO_SDA_PIN) && defined(VARIO_SCL_PIN)
  while(!ms5611.begin(VARIO_SDA_PIN, VARIO_SCL_PIN))
#else
  while(!ms5611.begin())
#endif
  {
    SerialPort.println("Could not find a valid MS5611 sensor, check wiring!");
    delay(500);
  }

  // Get reference pressure for relative altitude
  referencePressure = ms5611.readPressure();

  // Check settings
  checkSettings();
  
  // Call imu.begin() to verify communication and initialize
#if defined(VARIO_SDA_PIN) && defined(VARIO_SCL_PIN)
  if (imu.begin(VARIO_SDA_PIN, VARIO_SCL_PIN) != INV_SUCCESS)
#else
  if (imu.begin() != INV_SUCCESS)
#endif
  {
    while (1)
    {
      SerialPort.println("Unable to communicate with MPU-9250");
      SerialPort.println("Check connections, and try again.");
      SerialPort.println();
      delay(5000);
    }
  }
  
/*  imu.dmpBegin(DMP_FEATURE_6X_LP_QUAT | // Enable 6-axis quat
               DMP_FEATURE_GYRO_CAL, // Use gyro calibration
              10); // Set DMP FIFO rate to 10 Hz
  // DMP_FEATURE_LP_QUAT can also be used. It uses the 
  // accelerometer in low-power mode to estimate quat's.
  // DMP_FEATURE_LP_QUAT and 6X_LP_QUAT are mutually exclusive*/

  imu.setSensors(INV_XYZ_GYRO | INV_XYZ_ACCEL | INV_XYZ_COMPASS);

/*
  // Use setGyroFSR() and setAccelFSR() to configure the
  // gyroscope and accelerometer full scale ranges.
  // Gyro options are +/- 250, 500, 1000, or 2000 dps
  imu.setGyroFSR(2000); // Set gyro to 2000 dps
  // Accel options are +/- 2, 4, 8, or 16 g
  imu.setAccelFSR(8); // Set accel to +/-2g
  // Note: the MPU-9250's magnetometer FSR is set at 
  // +/- 4912 uT (micro-tesla's)

  // setLPF() can be used to set the digital low-pass filter
  // of the accelerometer and gyroscope.
  // Can be any of the following: 188, 98, 42, 20, 10, 5
  // (values are in Hz).
  imu.setLPF(5); // Set LPF corner frequency to 5Hz*/

  // The sample rate of the accel/gyro can be set using
  // setSampleRate. Acceptable values range from 4Hz to 1kHz
  imu.setSampleRate(100); // Set sample rate to 10Hz

  // Likewise, the compass (magnetometer) sample rate can be
  // set using the setCompassSampleRate() function.
  // This value can range between: 1-100Hz
  imu.setCompassSampleRate(100); // Set mag rate to 10Hz  
  imu.dmpBegin(DMP_FEATURE_SEND_RAW_ACCEL | // Send accelerometer data
 //              DMP_FEATURE_SEND_RAW_GYRO  | // Send raw gyroscope values to FIFO
               DMP_FEATURE_GYRO_CAL       | // Calibrate the gyro data
               DMP_FEATURE_SEND_CAL_GYRO  | // Send calibrated gyro data
               DMP_FEATURE_6X_LP_QUAT     , // Calculate quat's with accel/gyro
               100);                         // Set update rate to 10Hz.

#if defined(SAVE_EEPROM)
  accelBias[0]  = 257;
  accelBias[1]  = -793;
  accelBias[2]  = 324;
  
  gyroBias[3]   = -3;
  gyroBias[3]   = 13;
  gyroBias[3]   = 7;
  
  imu.set_accel_biases(accelBias);  
  imu.set_gyro_biases(gyroBias);
  imu.WriteEeprom();
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
