prunkdump/GNUVario-TTGO-T5/Photos/V1/20190727_122628.jpg

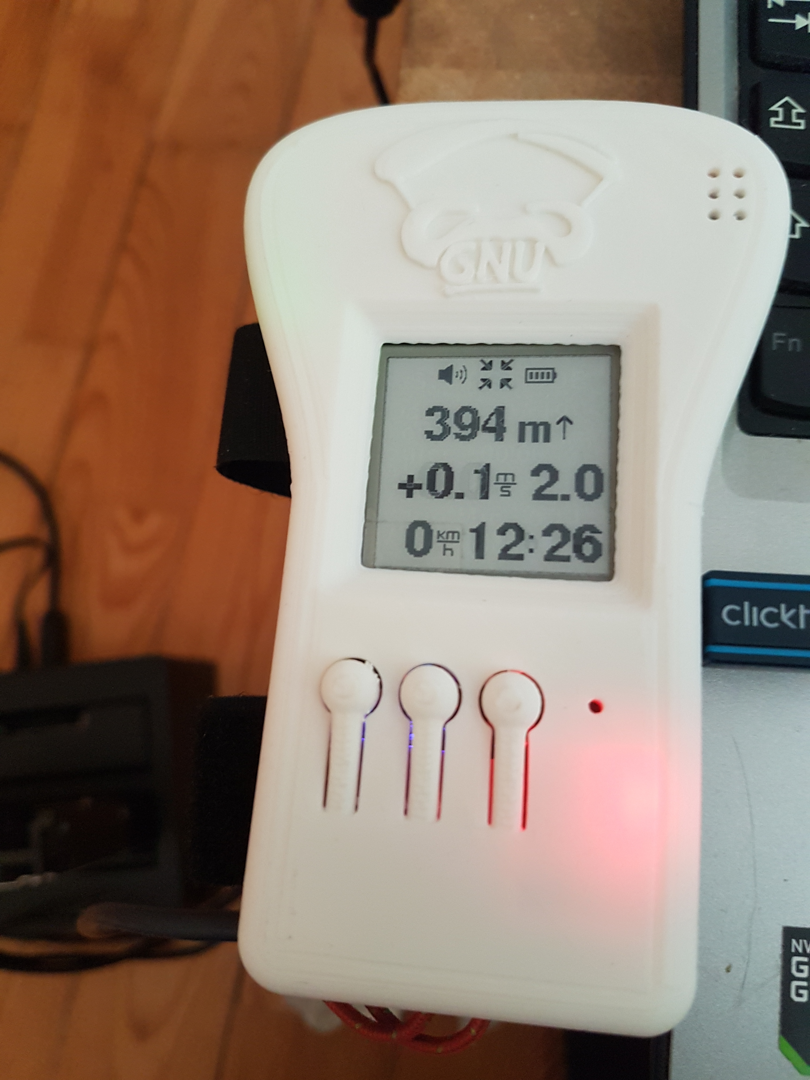
Photos/V1/20190727_122628.jpg
